fgervais/project-hw-60v-dcdc-module/assets/img/noise_5V/temperature_8V2A.jpg

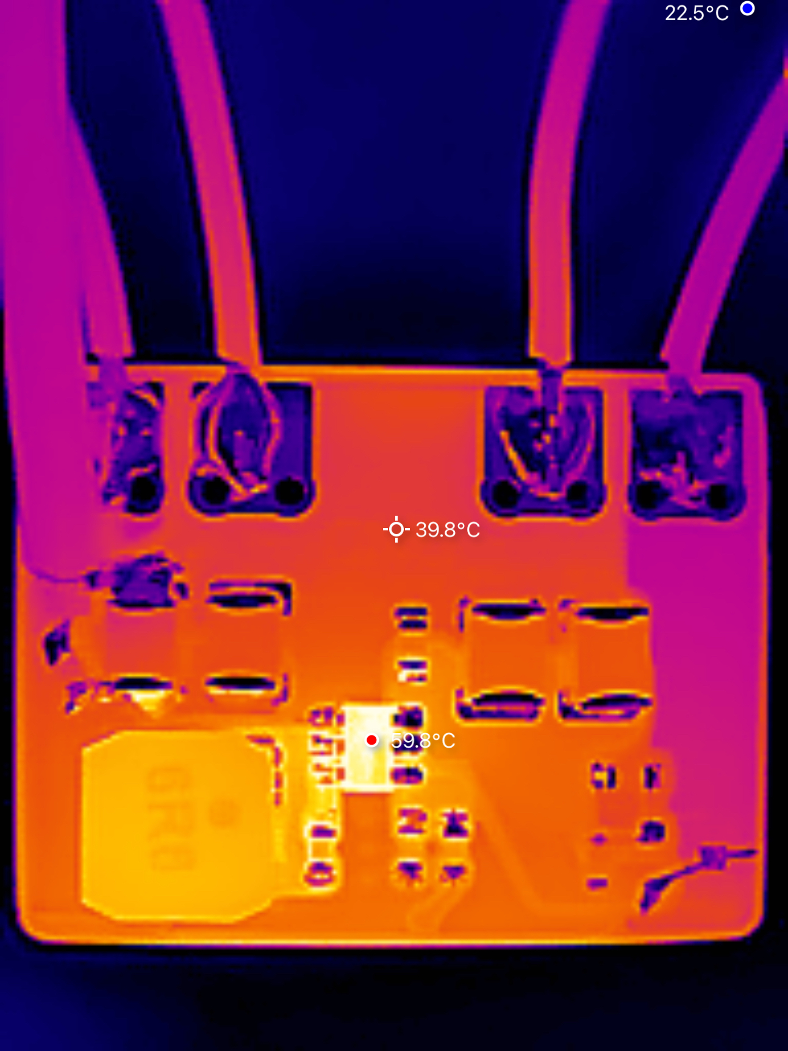
assets/img/noise_5V/temperature_8V2A.jpg
