fgervais/project-hw-60v-dcdc-module/assets/img/noise_5V/temperature_20V15A.jpg

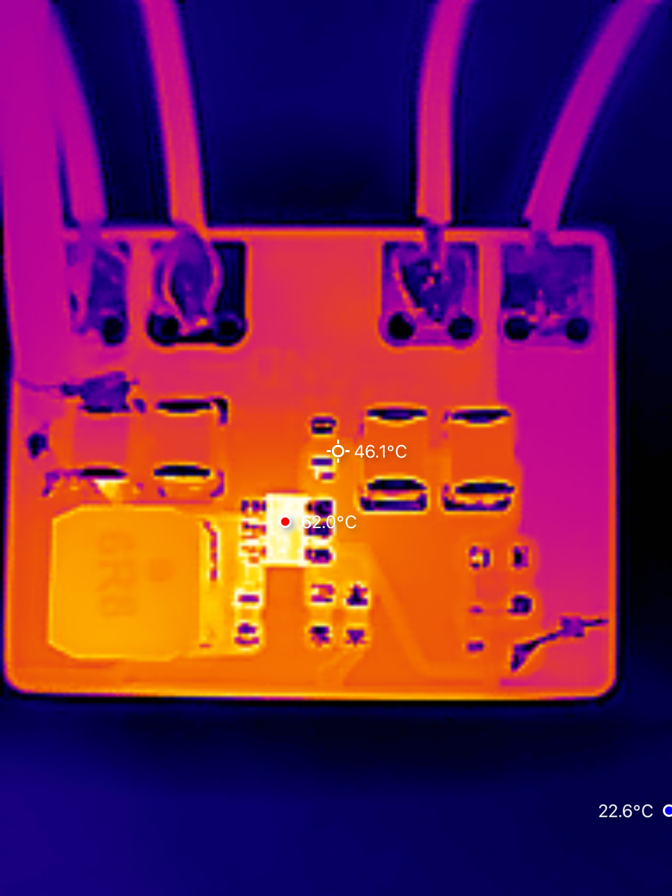
assets/img/noise_5V/temperature_20V15A.jpg
