fgervais/project-hw-60v-dcdc-module/assets/img/noise_5V/temperature_24V12A.jpg

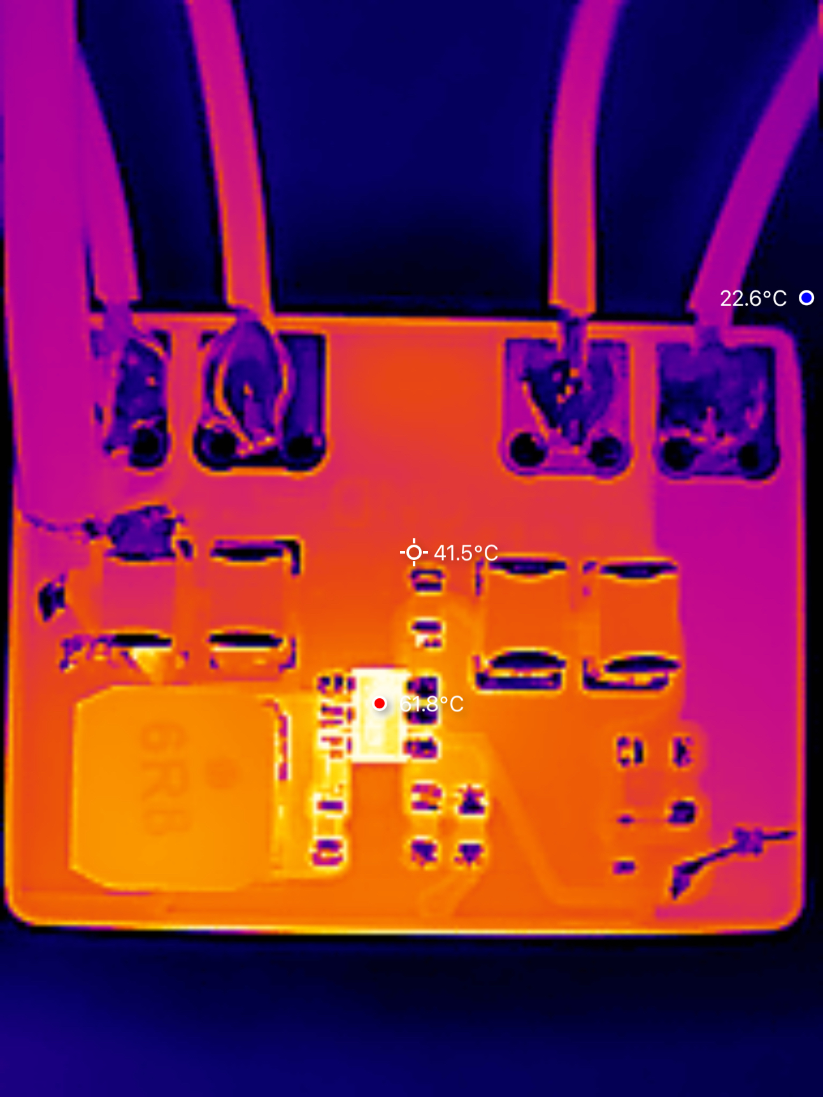
assets/img/noise_5V/temperature_24V12A.jpg
