fgervais/project-hw-60v-dcdc-module/assets/img/noise_5V/temperature_48V04A.jpg

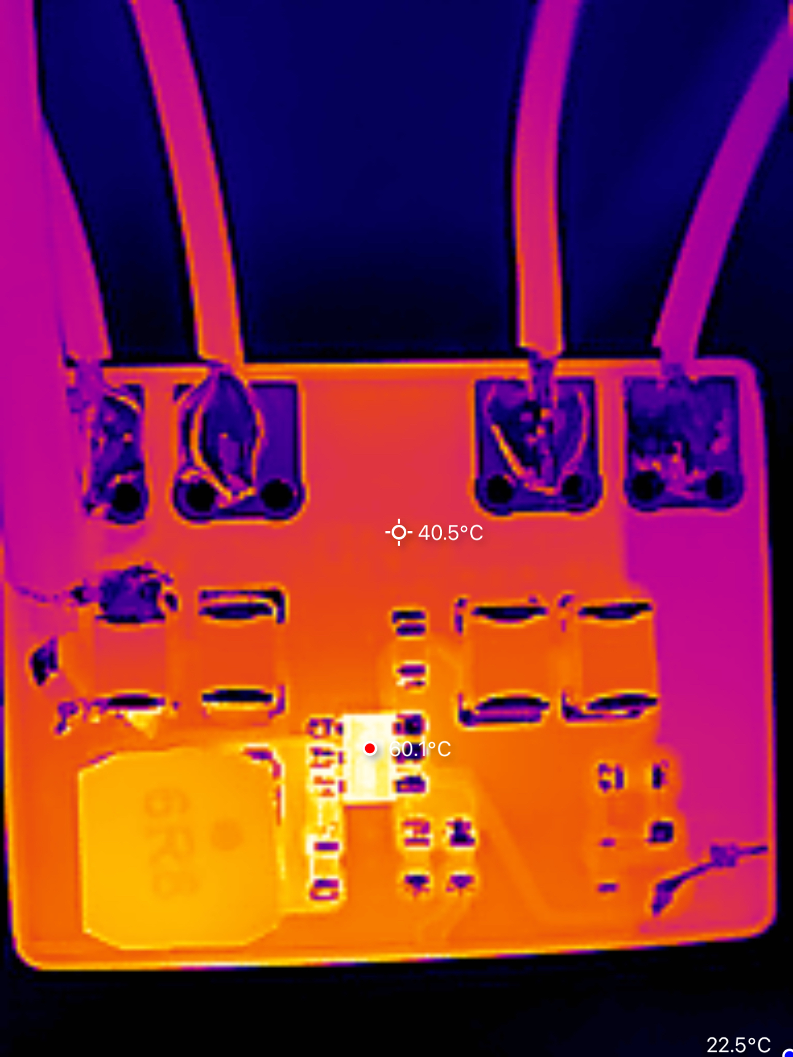
assets/img/noise_5V/temperature_48V04A.jpg
