fgervais/project-hw-60v-dcdc-module/assets/img/probe_overview.jpg

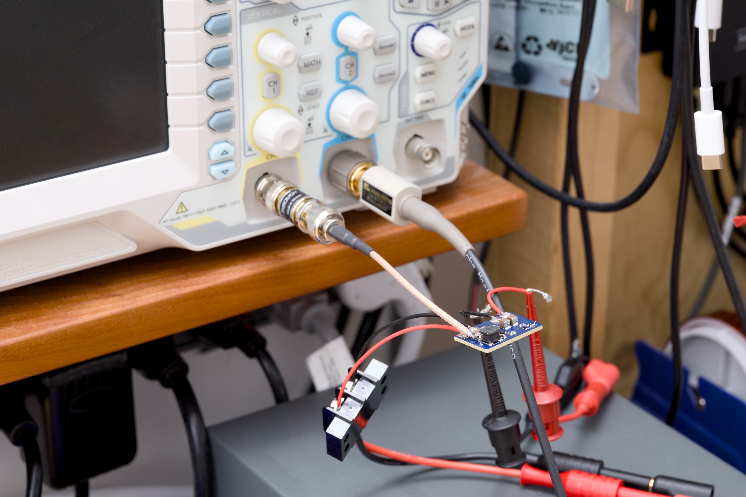
assets/img/probe_overview.jpg
