fgervais/project-hw-60v-dcdc-module/assets/img/probe_zoom.jpg

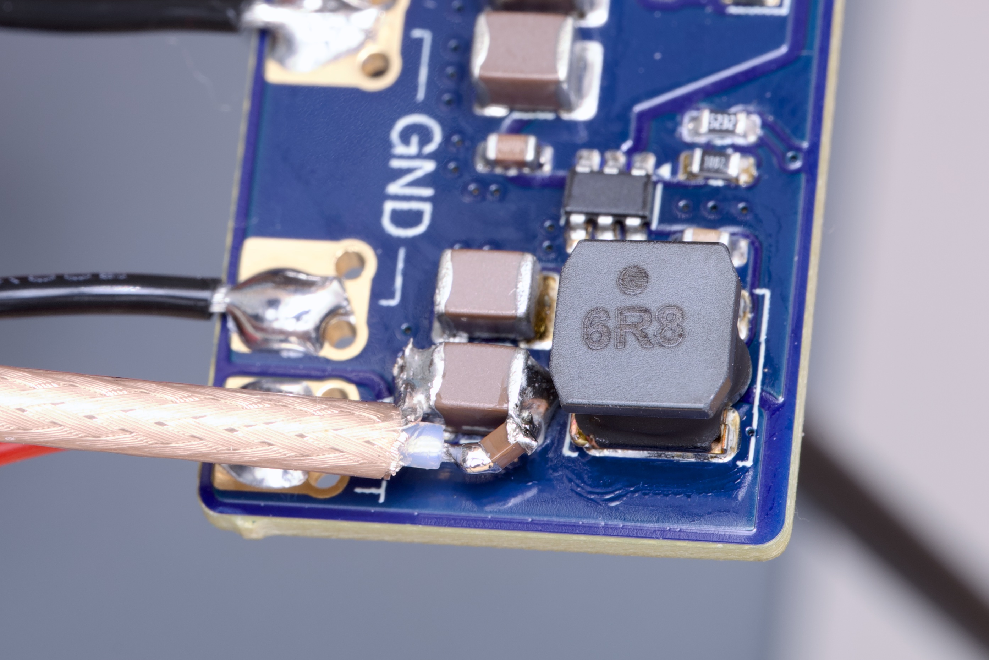
assets/img/probe_zoom.jpg
